TAMS-Group/tams_printed_ft/openscad/adjustable-ft-v1.png

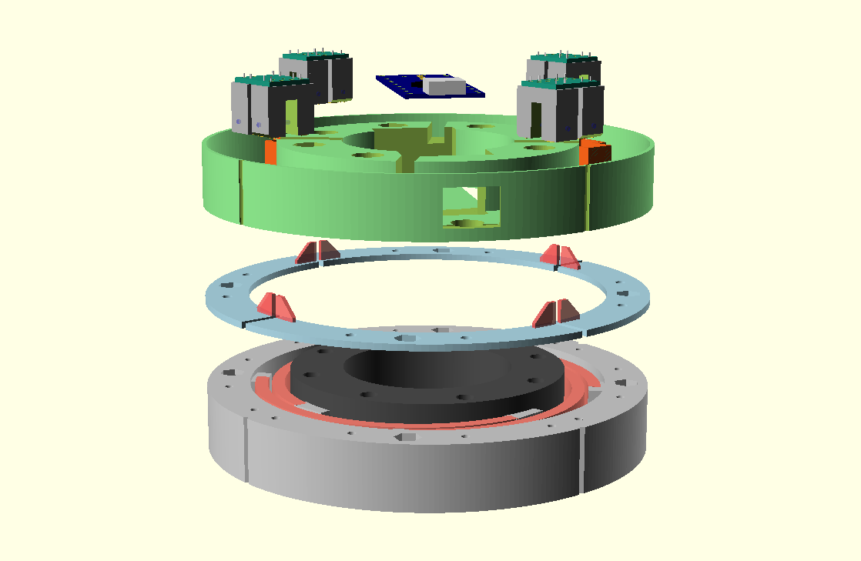
openscad/adjustable-ft-v1.png
