TAMS-Group/tams_printed_ft/openscad/spacemouse-9904.png

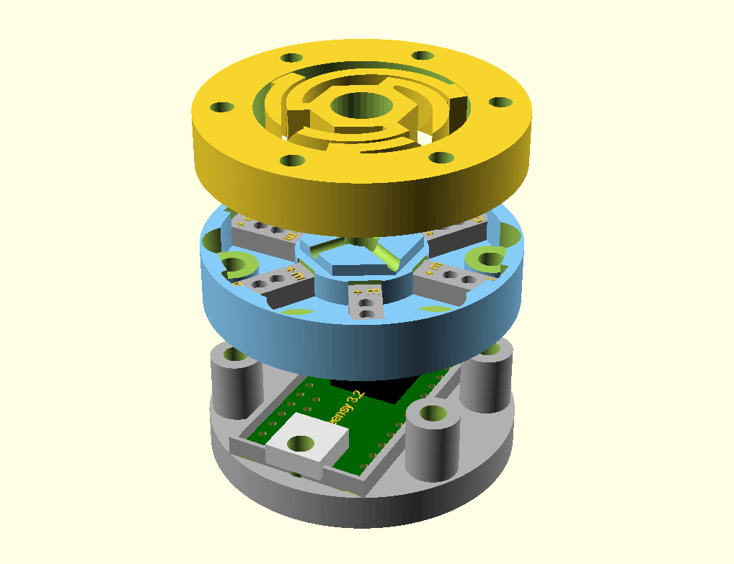
openscad/spacemouse-9904.png
