TAMS-Group/tams_printed_ft/openscad/stl/block-ft-cover-ring-40-height-10.stl

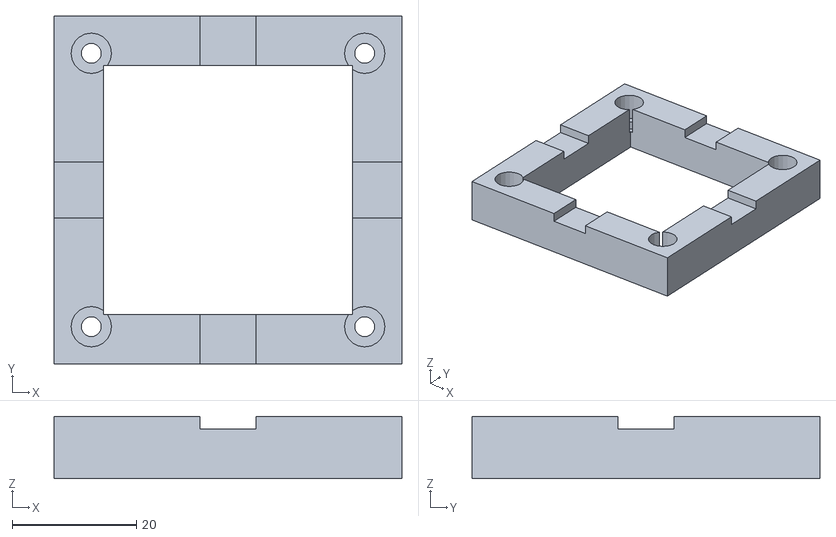
[picture p32: CAD file, 2020-05-22]
openscad/stl/block-ft-cover-ring-40-height-10.stl
56.0 x 56.0 x 10.0
