TAMS-Group/tams_printed_ft/openscad/stl/block-ft-x-07-10-15-y-07-7-z-06-10-6.stl

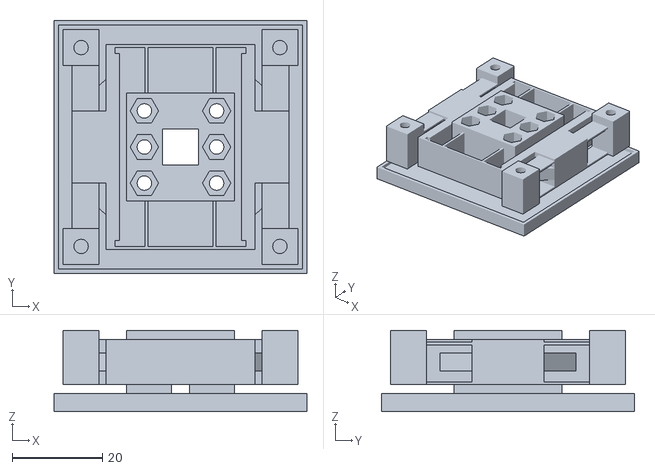
[picture p33: CAD file, 2020-05-22]
openscad/stl/block-ft-x-07-10-15-y-07-7-z-06-10-6.stl
56.0 x 56.0 x 18.0
