TAMS-Group/tams_printed_ft/openscad/stl/block-ft-cover-ring-40-height-8.stl

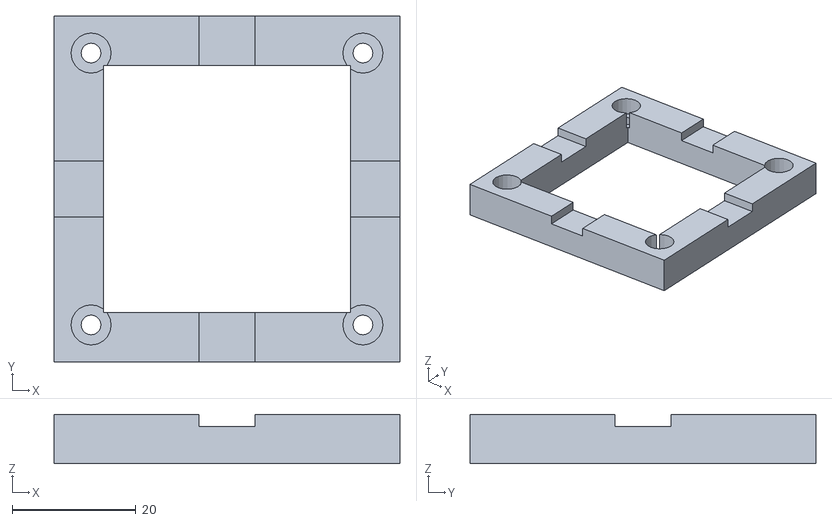
[picture p34: CAD file, 2020-05-22]
openscad/stl/block-ft-cover-ring-40-height-8.stl
56.0 x 56.0 x 8.00
