TAMS-Group/tams_printed_ft/openscad/stl/block-ft-base-holder.stl

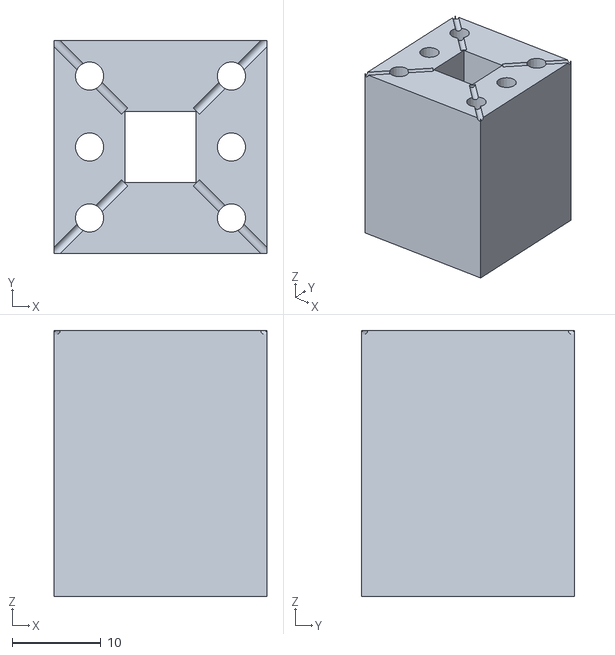
[picture p35: CAD file, 2020-05-22]
openscad/stl/block-ft-base-holder.stl
24.0 x 24.0 x 30.0
