TAMS-Group/tams_printed_ft/openscad/stl/block-ft-fake-pcb-40.stl

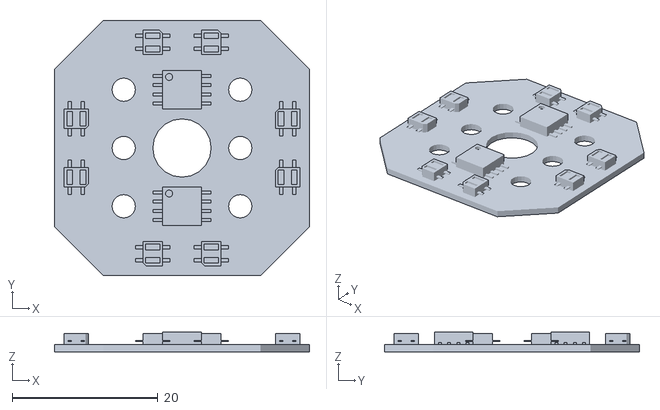
[picture p36: CAD file, 2020-05-22]
openscad/stl/block-ft-fake-pcb-40.stl
35.0 x 35.0 x 2.70
