TAMS-Group/tams_printed_ft/openscad/stl/block-ft-pattern-plate-40.stl

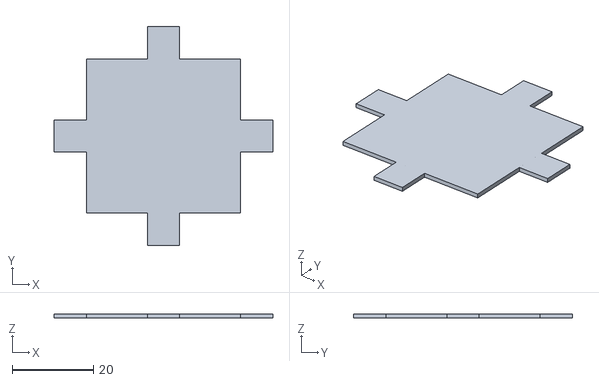
[picture p37: CAD file, 2020-05-22]
openscad/stl/block-ft-pattern-plate-40.stl
54.0 x 54.0 x 1.00
