TAMS-Group/tams_printed_ft/openscad/stl/block-ft-base-plate.stl

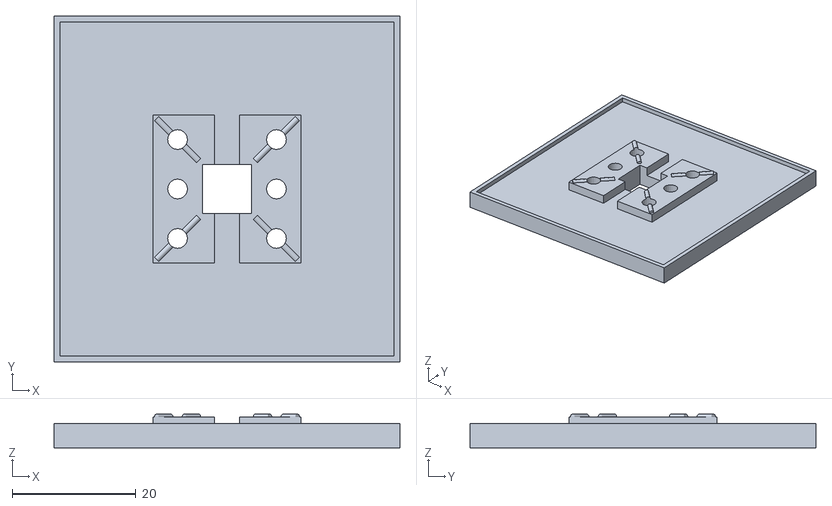
[picture p38: CAD file, 2020-05-22]
openscad/stl/block-ft-base-plate.stl
56.0 x 56.0 x 5.50
