TAMS-Group/tams_printed_ft/openscad/stl/block-ft-cover-ring-40-height-9.stl

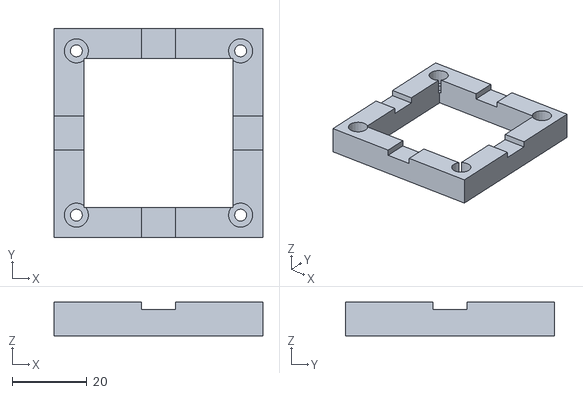
[picture p39: CAD file, 2020-05-22]
openscad/stl/block-ft-cover-ring-40-height-9.stl
56.0 x 56.0 x 9.00
