TAMS-Group/tams_printed_ft/openscad/stl/block-ft-x-07-10-9-y-07-10-z-06-10-8.stl

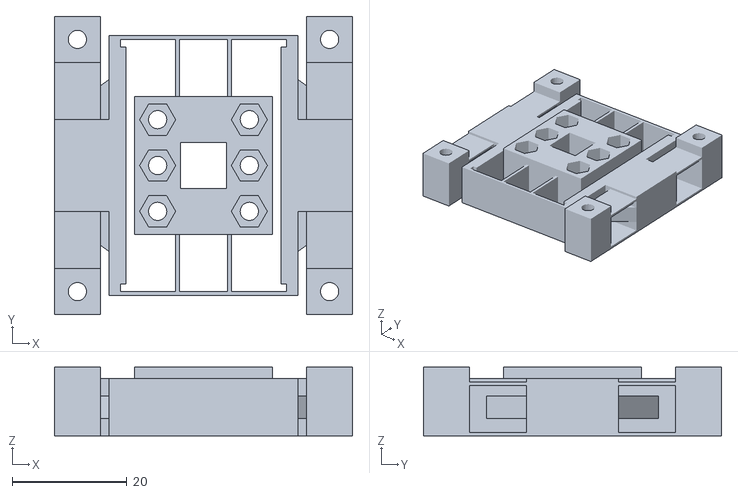
[picture p40: CAD file, 2020-05-22]
openscad/stl/block-ft-x-07-10-9-y-07-10-z-06-10-8.stl
52.0 x 52.0 x 12.0
