TAMS-Group/tams_printed_ft/openscad/stl/block-ft-m3207-adapter-outer.stl

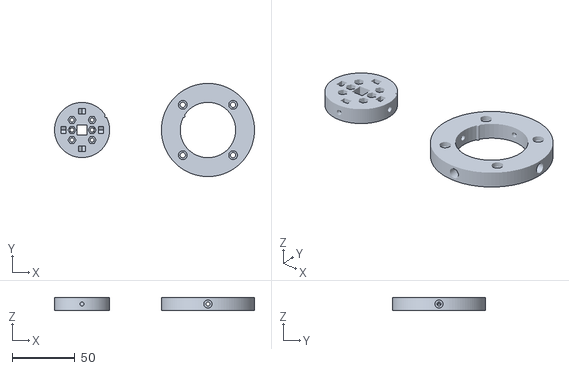
[picture p41: CAD file, 2020-05-22]
openscad/stl/block-ft-m3207-adapter-outer.stl
158.9 x 74.0 x 10.0
