TAMS-Group/tams_printed_ft/openscad/stl/ft-pushing-box-sensor-carrier.stl

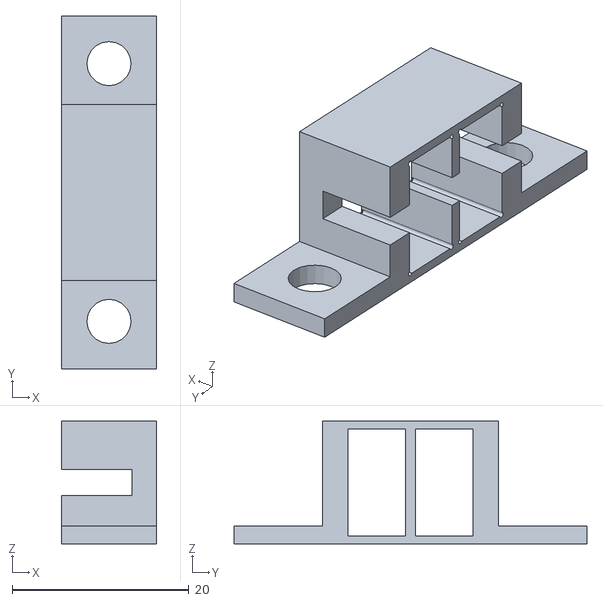
[picture p42: CAD file, 2020-05-20]
openscad/stl/ft-pushing-box-sensor-carrier.stl
10.8 x 40.0 x 13.9
