TAMS-Group/tams_printed_ft/openscad/stl/ft-pushing-box-coins-holder.stl

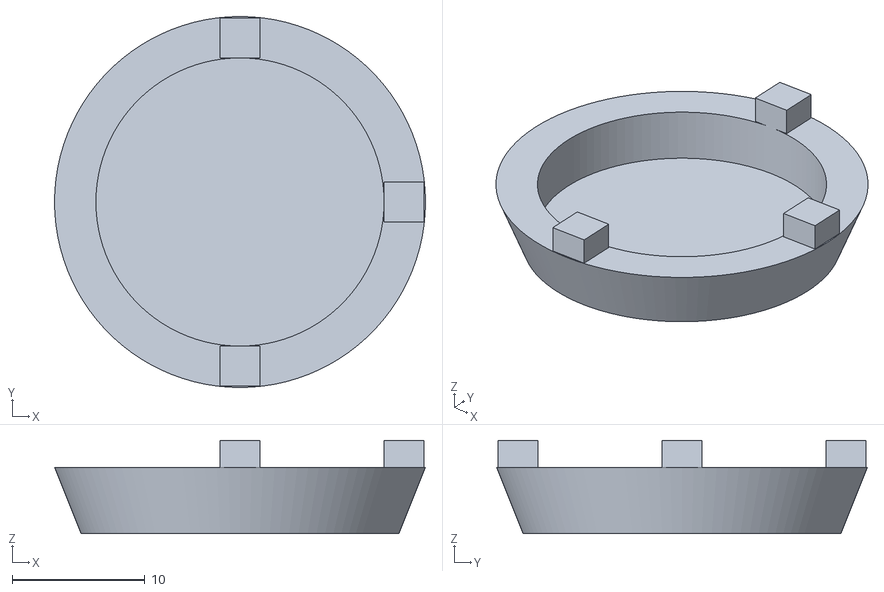
[picture p43: CAD file, 2020-05-20]
openscad/stl/ft-pushing-box-coins-holder.stl
28.0 x 28.0 x 7.03
