TAMS-Group/tams_printed_ft/openscad/stl/ft-pushing-box-spring-block-v3.stl

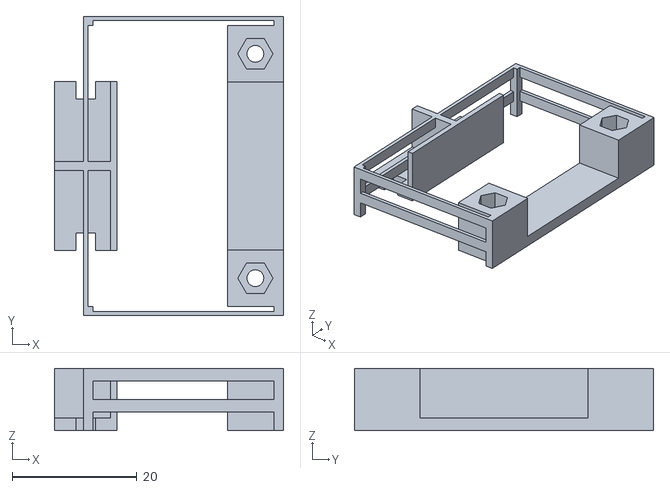
[picture p44: CAD file, 2020-05-20]
openscad/stl/ft-pushing-box-spring-block-v3.stl
36.6 x 47.9 x 10.0
