TAMS-Group/tams_printed_ft/openscad/stl/ft-pushing-box-bottom-plate.stl

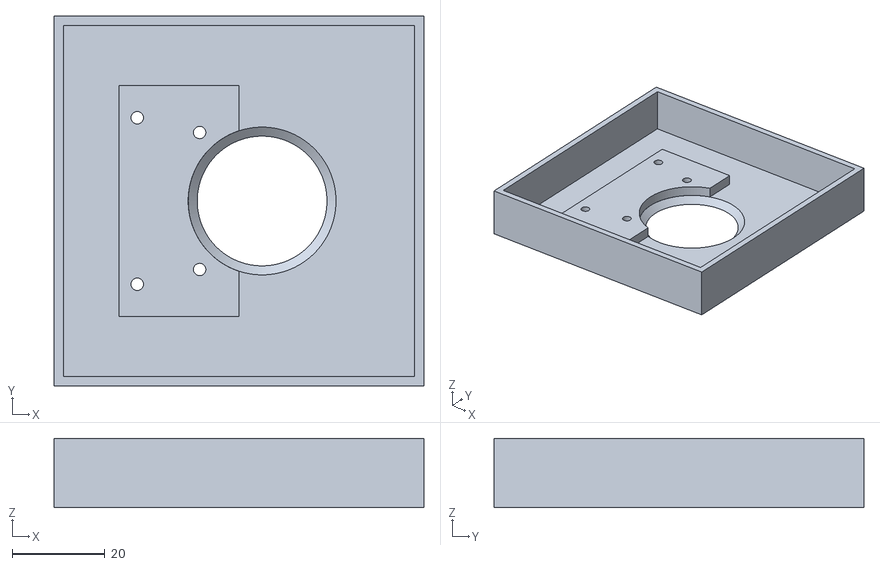
[picture p45: CAD file, 2020-05-20]
openscad/stl/ft-pushing-box-bottom-plate.stl
80.0 x 80.0 x 15.0
