TAMS-Group/tams_printed_ft/openscad/stl/ft-pushing-box-fin-carrier.stl

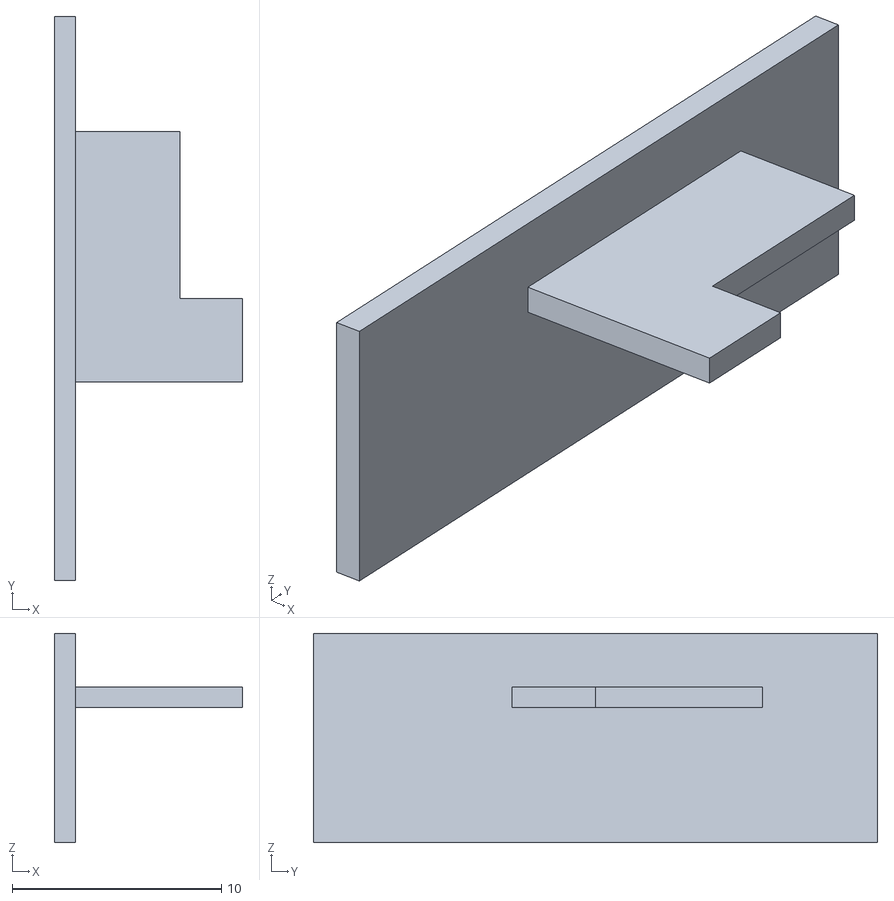
[picture p46: CAD file, 2020-05-20]
openscad/stl/ft-pushing-box-fin-carrier.stl
9.00 x 27.0 x 10.0
