TAMS-Group/tams_printed_ft/openscad/stl/ft-pushing-box-spring-block.stl

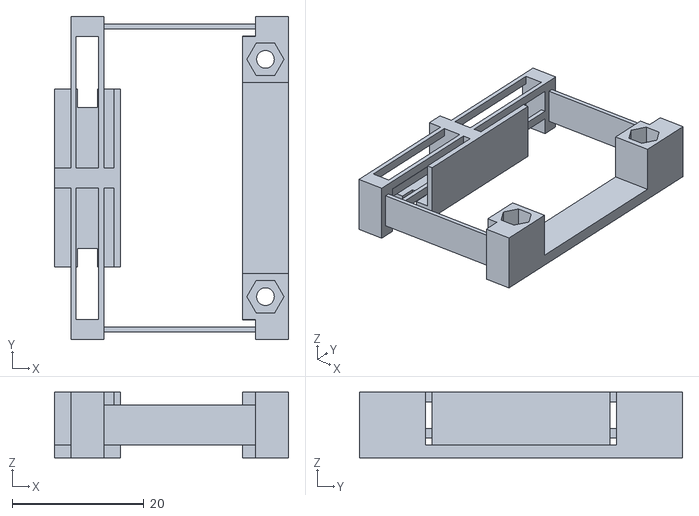
[picture p47: CAD file, 2020-05-20]
openscad/stl/ft-pushing-box-spring-block.stl
35.5 x 49.0 x 10.0
