TAMS-Group/tams_printed_ft/openscad/stl/2DOF_soldering_tool.stl

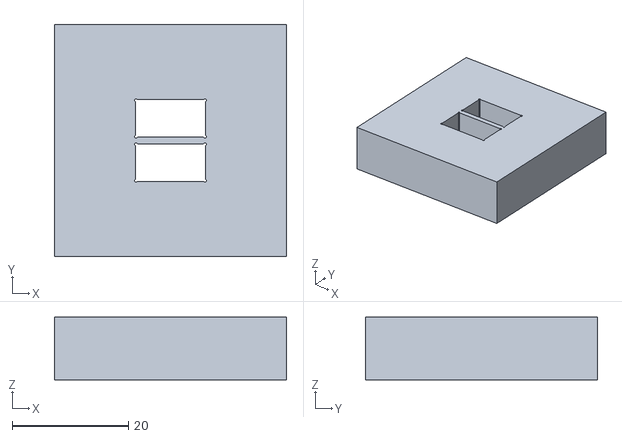
[picture p48: CAD file, 2020-05-18]
openscad/stl/2DOF_soldering_tool.stl
40.0 x 40.0 x 10.8
